Fabiancrg/caelum-weatherstation/main/esp_zb_weather.h

/*
 * SPDX-FileCopyrightText: 2021-2024 Espressif Systems (Shanghai) CO LTD
 *
 * SPDX-License-Identifier:  LicenseRef-Included
 *
 * Zigbee HA_on_off_light Example
 *
 * This example code is in the Public Domain (or CC0 licensed, at your option.)
 *
 * Unless required by applicable law or agreed to in writing, this
 * software is distributed on an "AS IS" BASIS, WITHOUT WARRANTIES OR
 * CONDITIONS OF ANY KIND, either express or implied.
 */

#include "esp_zigbee_core.h"
#include "zcl_utility.h"

/* Zigbee configuration */
#define INSTALLCODE_POLICY_ENABLE       false                                /* enable the install code policy for security */
#define ED_AGING_TIMEOUT                ESP_ZB_ED_AGING_TIMEOUT_8MIN         /* aging timeout for sleepy end device */
#define ED_KEEP_ALIVE                   15000                                /* 15000 millisecond - poll parent every 15s */
#define HA_ESP_BME280_ENDPOINT          1                                    /* esp BME280 environmental sensor endpoint */
#define HA_ESP_RAIN_GAUGE_ENDPOINT      2                                    /* esp rain gauge sensor endpoint */
#define HA_ESP_SLEEP_CONFIG_ENDPOINT    3                                    /* esp sleep configuration endpoint */
#define HA_ESP_LED_DEBUG_ENDPOINT       4                                    /* esp LED debug control endpoint (genOnOff) */
#define ESP_ZB_PRIMARY_CHANNEL_MASK     ESP_ZB_TRANSCEIVER_ALL_CHANNELS_MASK /* Zigbee primary channel mask use in the example */

/* Debug LED configuration */
#define DEBUG_LED_ENABLE                1                                    /* Set to 1 to enable LED debug indicator */
#define DEBUG_LED_TYPE_RGB              1                                    /* Set to 1 for WS2812 RGB LED, 0 for simple GPIO */
#ifdef CONFIG_IDF_TARGET_ESP32H2
#define DEBUG_LED_GPIO                  GPIO_NUM_8                           /* Built-in RGB LED on ESP32-H2 SuperMini */
#else
#define DEBUG_LED_GPIO                  GPIO_NUM_8                           /* Adjust for your board */
#endif

/* Deep sleep configuration for battery operation */
#define SLEEP_DURATION_MINUTES          15                                   /* Wake up every 15 minutes for periodic reporting */
#define SLEEP_DURATION_S                (SLEEP_DURATION_MINUTES * 60)
#ifdef CONFIG_IDF_TARGET_ESP32H2
#define RAIN_WAKE_GPIO                  GPIO_NUM_12                          /* GPIO for rain gauge wake-up (RTC-capable on ESP32-H2) */
#else
#define RAIN_WAKE_GPIO                  GPIO_NUM_5                           /* GPIO for rain gauge wake-up (RTC-capable on ESP32-C6) */
#endif
#define RAIN_MM_THRESHOLD               1.0f                                 /* Wake up immediately if rain > 1mm */

/* Basic manufacturer information - now using CMakeLists.txt definitions */
#define ESP_MANUFACTURER_NAME "\x09""ESPRESSIF"      /* Customized manufacturer name */
#define ESP_MODEL_IDENTIFIER "\x06""caelum"          /* Customized model identifier matching CMakeLists.txt project name */

/* Firmware version information */
#ifdef FW_VERSION
#define FIRMWARE_VERSION_STRING         FW_VERSION                           /* From CMakeLists.txt */
#else
#define FIRMWARE_VERSION_STRING         "0.1.0"                              /* Default version */
#endif

#define ESP_ZB_ZED_CONFIG()                                         \
    {                                                               \
        .esp_zb_role = ESP_ZB_DEVICE_TYPE_ED,                       \
        .install_code_policy = INSTALLCODE_POLICY_ENABLE,           \
        .nwk_cfg.zed_cfg = {                                        \
            .ed_timeout = ED_AGING_TIMEOUT,                         \
            .keep_alive = ED_KEEP_ALIVE,                            \
        },                                                          \
    }

#define ESP_ZB_DEFAULT_RADIO_CONFIG()                           \
    {                                                           \
        .radio_mode = ZB_RADIO_MODE_NATIVE,                     \
    }

#define ESP_ZB_DEFAULT_HOST_CONFIG()                            \
    {                                                           \
        .host_connection_mode = ZB_HOST_CONNECTION_MODE_NONE,   \
    }
